fukayatsu/laptop-keyball61-case/scad/keyball61_outline.scad

// 自動生成: scripts/extract_outline.py による Keyball61 BallSide 底板の実寸データ
// 座標系: 左手ユニットを上から見た形 / 原点=外形バウンディングボックスの南西角 / +Y=奥(北)
// 編集しないこと。再生成: python3 scripts/extract_outline.py <DXF>
plate_w = 142.99;
plate_d = 113.53;
plate_outline = [
  [70.469,105.952],
  [71.227,105.880],
  [80.812,104.031],
  [81.588,103.958],
  [100.075,104.045],
  [100.583,104.091],
  [119.410,107.418],
  [119.914,107.553],
  [136.160,113.466],
  [136.328,113.511],
  [136.502,113.527],
  [136.676,113.511],
  [136.844,113.466],
  [137.002,113.393],
  [137.145,113.293],
  [137.268,113.169],
  [137.368,113.027],
  [137.442,112.869],
  [142.931,97.786],
  [142.980,97.597],
  [142.990,97.401],
  [142.963,97.207],
  [142.898,97.022],
  [142.798,96.853],
  [142.667,96.707],
  [142.510,96.589],
  [142.334,96.505],
  [134.323,93.589],
  [133.849,93.368],
  [133.421,93.068],
  [133.051,92.698],
  [132.751,92.270],
  [132.530,91.796],
  [132.395,91.291],
  [132.349,90.770],
  [132.349,66.014],
  [132.366,65.834],
  [132.414,65.660],
  [132.493,65.498],
  [132.600,65.353],
  [132.731,65.228],
  [132.882,65.130],
  [133.048,65.060],
  [133.215,64.991],
  [133.367,64.892],
  [133.498,64.768],
  [133.604,64.623],
  [133.683,64.461],
  [133.732,64.286],
  [133.748,64.107],
  [133.748,29.050],
  [133.748,6.000],
  [133.729,5.805],
  [133.672,5.618],
  [133.580,5.445],
  [133.455,5.293],
  [133.304,5.169],
  [133.131,5.076],
  [132.943,5.019],
  [132.748,5.000],
  [95.252,5.000],
  [95.056,4.981],
  [94.869,4.925],
  [94.696,4.832],
  [94.544,4.707],
  [94.420,4.556],
  [94.328,4.383],
  [94.271,4.195],
  [94.252,4.001],
  [94.252,3.501],
  [94.232,3.305],
  [94.175,3.118],
  [94.083,2.945],
  [93.959,2.793],
  [93.807,2.669],
  [93.634,2.577],
  [93.447,2.520],
  [93.251,2.500],
  [76.201,2.500],
  [76.006,2.481],
  [75.819,2.424],
  [75.646,2.332],
  [75.494,2.207],
  [75.370,2.056],
  [75.277,1.883],
  [75.220,1.696],
  [75.201,1.500],
  [75.201,1.001],
  [75.182,0.805],
  [75.125,0.617],
  [75.033,0.445],
  [74.908,0.293],
  [74.757,0.169],
  [74.584,0.077],
  [74.396,0.019],
  [74.201,0.000],
  [58.151,0.000],
  [57.977,0.015],
  [57.809,0.061],
  [57.651,0.134],
  [57.508,0.234],
  [57.385,0.358],
  [57.285,0.500],
  [57.211,0.658],
  [57.166,0.827],
  [57.151,1.001],
  [57.151,3.700],
  [57.132,3.895],
  [57.075,4.083],
  [56.982,4.256],
  [56.858,4.407],
  [56.706,4.532],
  [56.534,4.624],
  [56.346,4.681],
  [56.151,4.700],
  [39.101,4.700],
  [38.927,4.715],
  [38.758,4.761],
  [38.600,4.834],
  [38.458,4.935],
  [38.334,5.057],
  [38.235,5.200],
  [38.161,5.358],
  [38.116,5.527],
  [38.101,5.700],
  [38.101,10.700],
  [38.081,10.895],
  [38.024,11.083],
  [37.932,11.256],
  [37.808,11.408],
  [37.656,11.532],
  [37.483,11.624],
  [37.296,11.681],
  [37.101,11.701],
  [19.050,11.701],
  [1.000,11.701],
  [0.805,11.720],
  [0.617,11.777],
  [0.445,11.869],
  [0.293,11.993],
  [0.168,12.145],
  [0.076,12.317],
  [0.019,12.506],
  [0.000,12.701],
  [0.000,104.952],
  [0.015,105.125],
  [0.060,105.294],
  [0.134,105.452],
  [0.234,105.595],
  [0.357,105.718],
  [0.500,105.818],
  [0.658,105.892],
  [0.826,105.937],
  [1.000,105.952],
  [19.050,105.952]
];
// [x, y, 直径] : d=11.3 はボール取出し穴, d=2.08 は M2, d=2.36 はボールケース部
plate_holes = [
  [71.961,95.252,12.0],
  [61.104,103.252,2.5],
  [61.104,87.252,2.5],
  [56.455,61.351,2.2],
  [128.785,88.912,2.2],
  [57.292,18.55,2.2],
  [18.773,87.402,2.2],
  [18.773,30.251,2.2],
  [94.556,21.051,2.2],
  [95.392,61.651,2.2],
  [120.871,101.715,2.2]
];
