fukayatsu/laptop-keyball61-case/scad/touchid/parts_touchid_foot.scad

include <touchid_foot.scad>
// 上下ともフラットな2mm板。ベタ置き(サポート不要)
touchid_foot();
