fukayatsu/laptop-keyball61-case/scad/touchid/parts_touchid_plate.scad

include <touchid_plate.scad>
// 底面(フットが付く側)をベッドに置いて印刷。天面のボスは0.15mmの島なのでサポート不要。
// ボスを再現するため積層は0.15mm以下にすること
touchid_plate();
