fukayatsu/laptop-keyball61-case/scad/v4/parts_v4_plate_left.scad

include <v4_plate.scad>
// 平面をベタ置き印刷(下面フラット・フェンスが上)
v4_plate_left();
